ThKattanek/1541-rebuild/doc/fotos/byte_ready_cut_gatearray.jpg

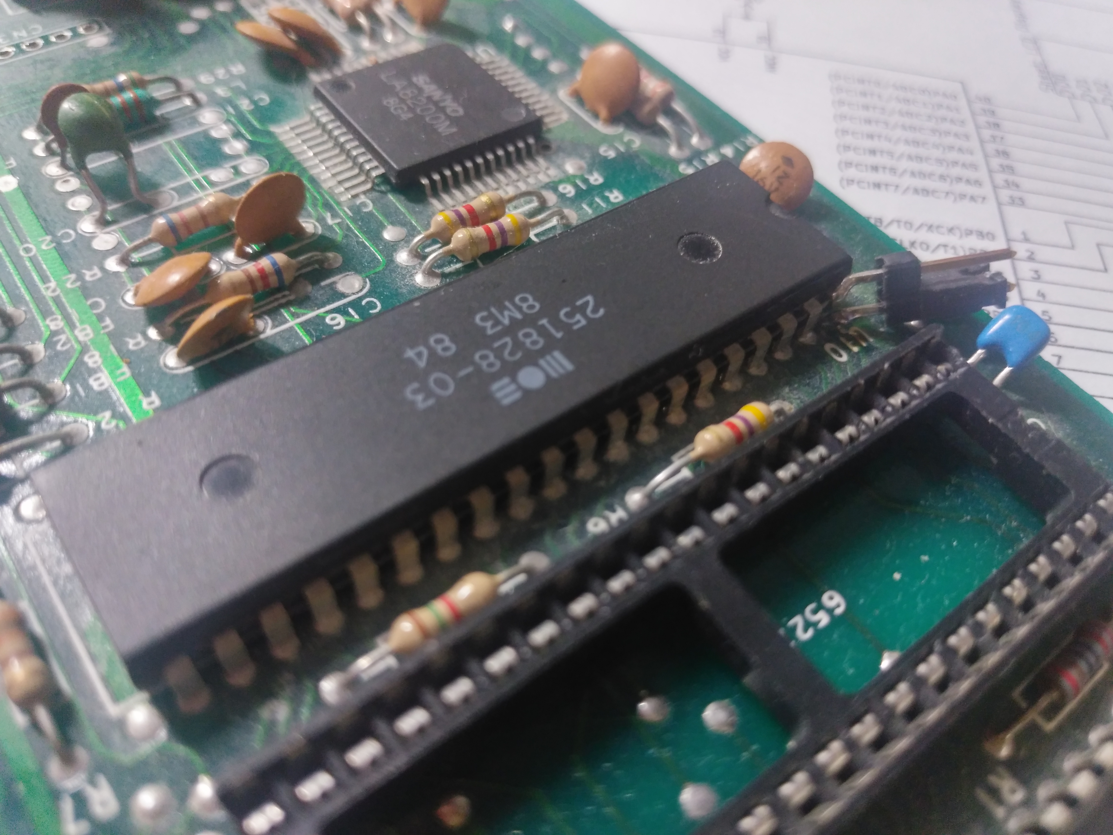
doc/fotos/byte_ready_cut_gatearray.jpg
