ThKattanek/1541-rebuild/doc/fotos/platine_rev_1.4.0/IMG_20200430_232406.jpg

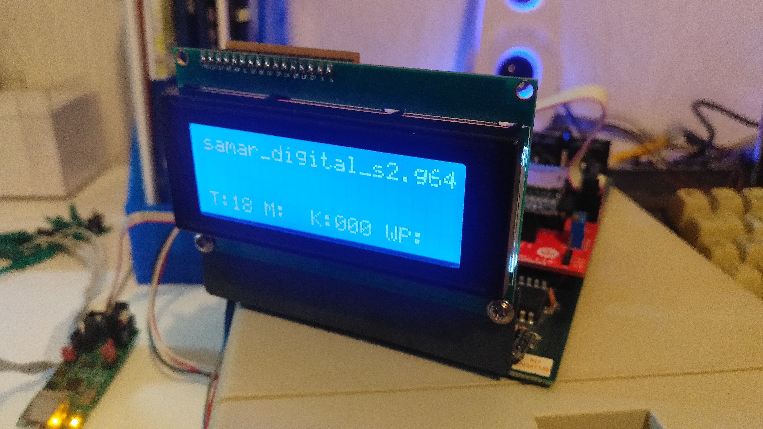
doc/fotos/platine_rev_1.4.0/IMG_20200430_232406.jpg
