ThKattanek/1541-rebuild/doc/fotos/prototyp_lochraster_v1.1/IMG_20180418_214337.jpg

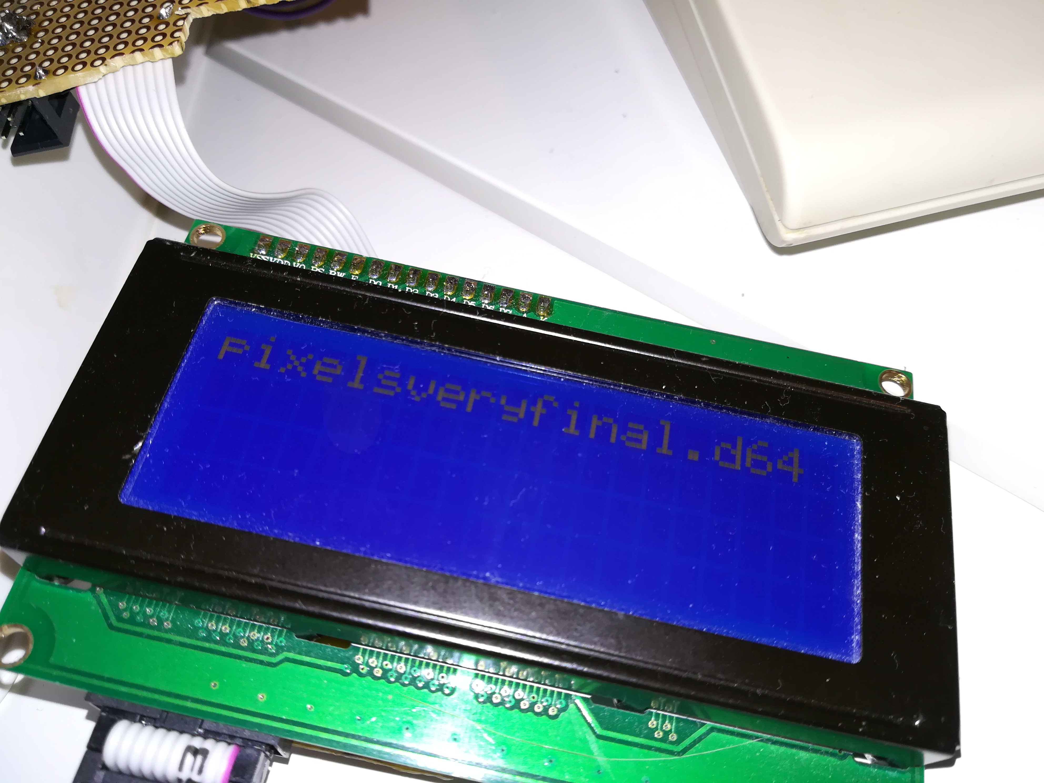
doc/fotos/prototyp_lochraster_v1.1/IMG_20180418_214337.jpg
