ThKattanek/1541-rebuild/doc/gesammelte_infos/1541-II.340503.gif

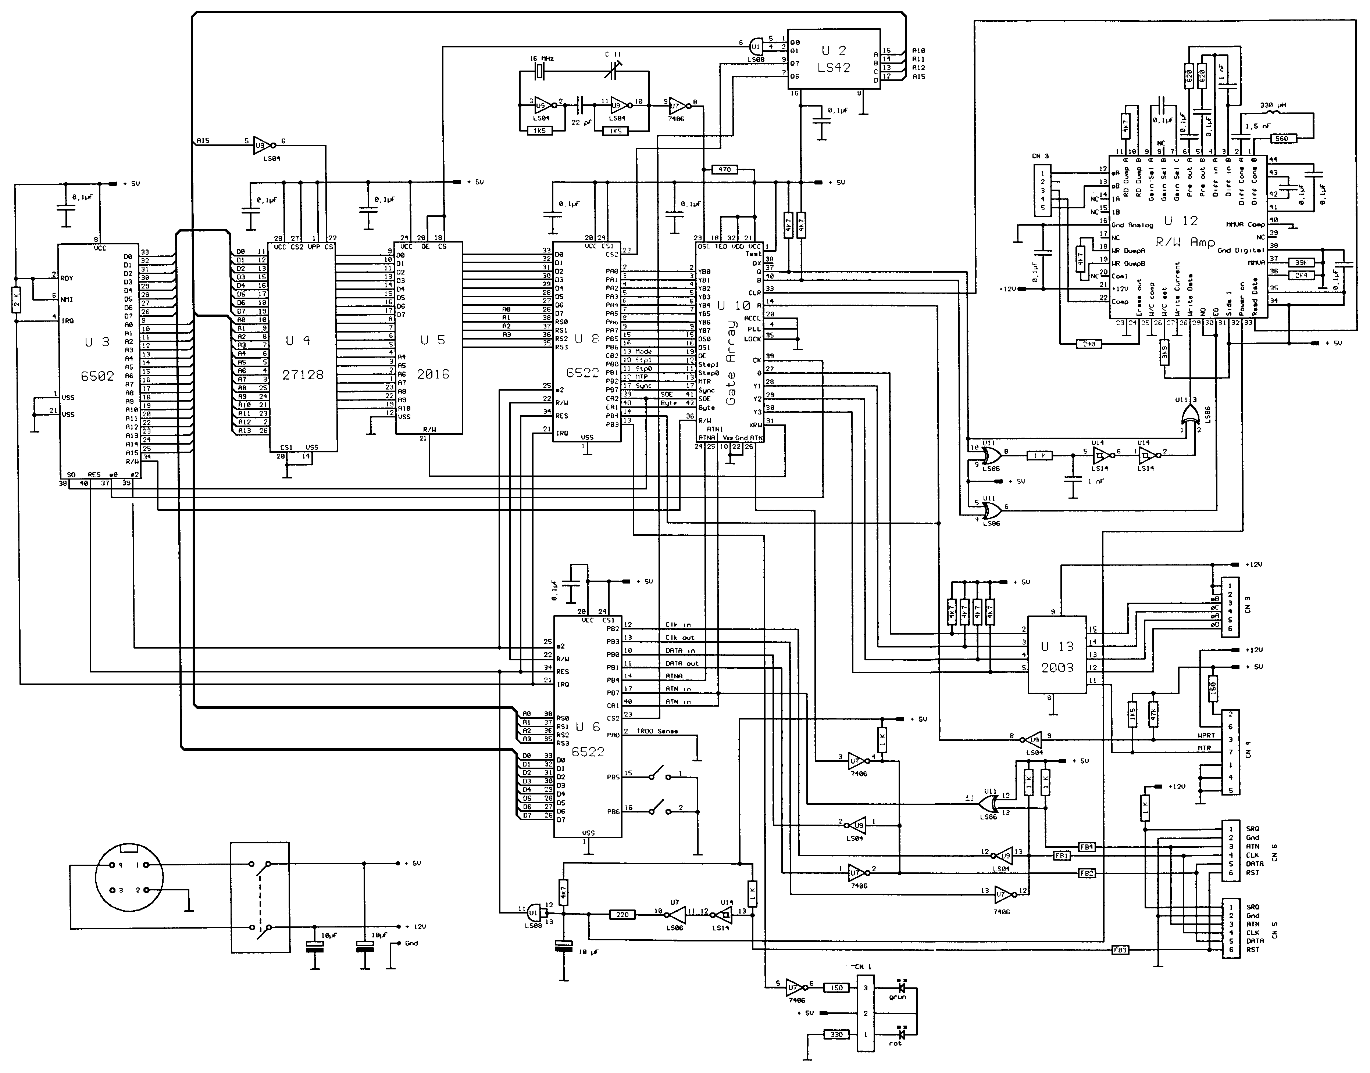
doc/gesammelte_infos/1541-II.340503.gif
