ThKattanek/1541-rebuild/doc/gesammelte_infos/1541-II_Schaltplan.gif

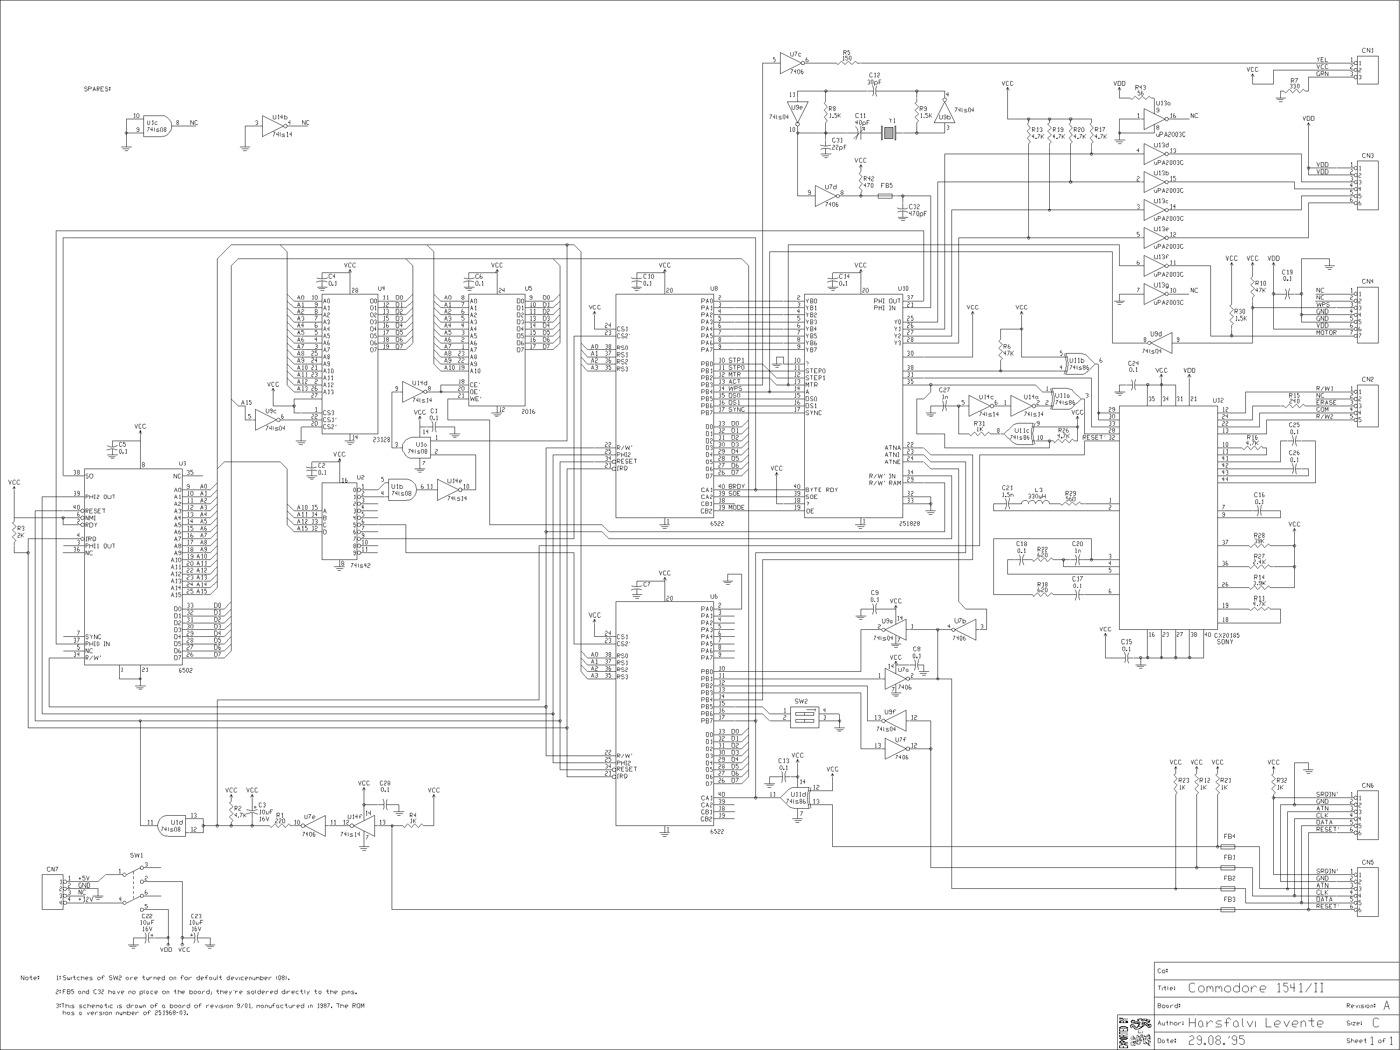
doc/gesammelte_infos/1541-II_Schaltplan.gif
