ThKattanek/1541-rebuild/doc/gesammelte_infos/1541_II_platinenaße_max.jpg

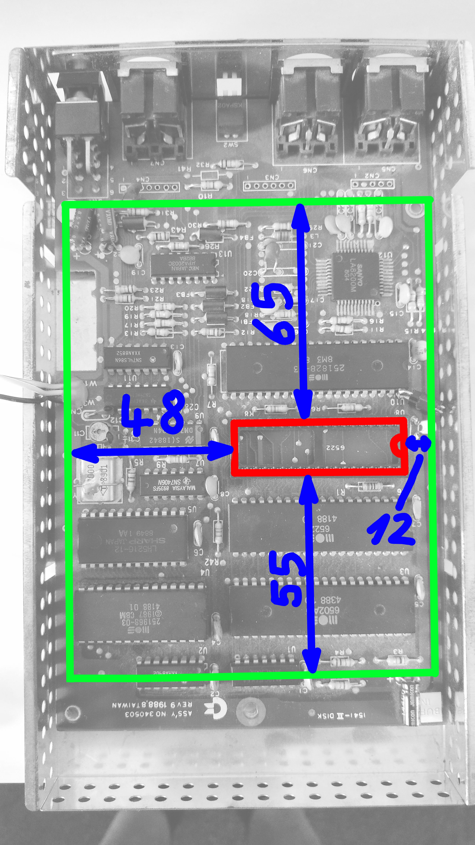
doc/gesammelte_infos/1541_II_platinenaße_max.jpg
