ThKattanek/1541-rebuild/doc/gesammelte_infos/mos_6522/6522-15.gif

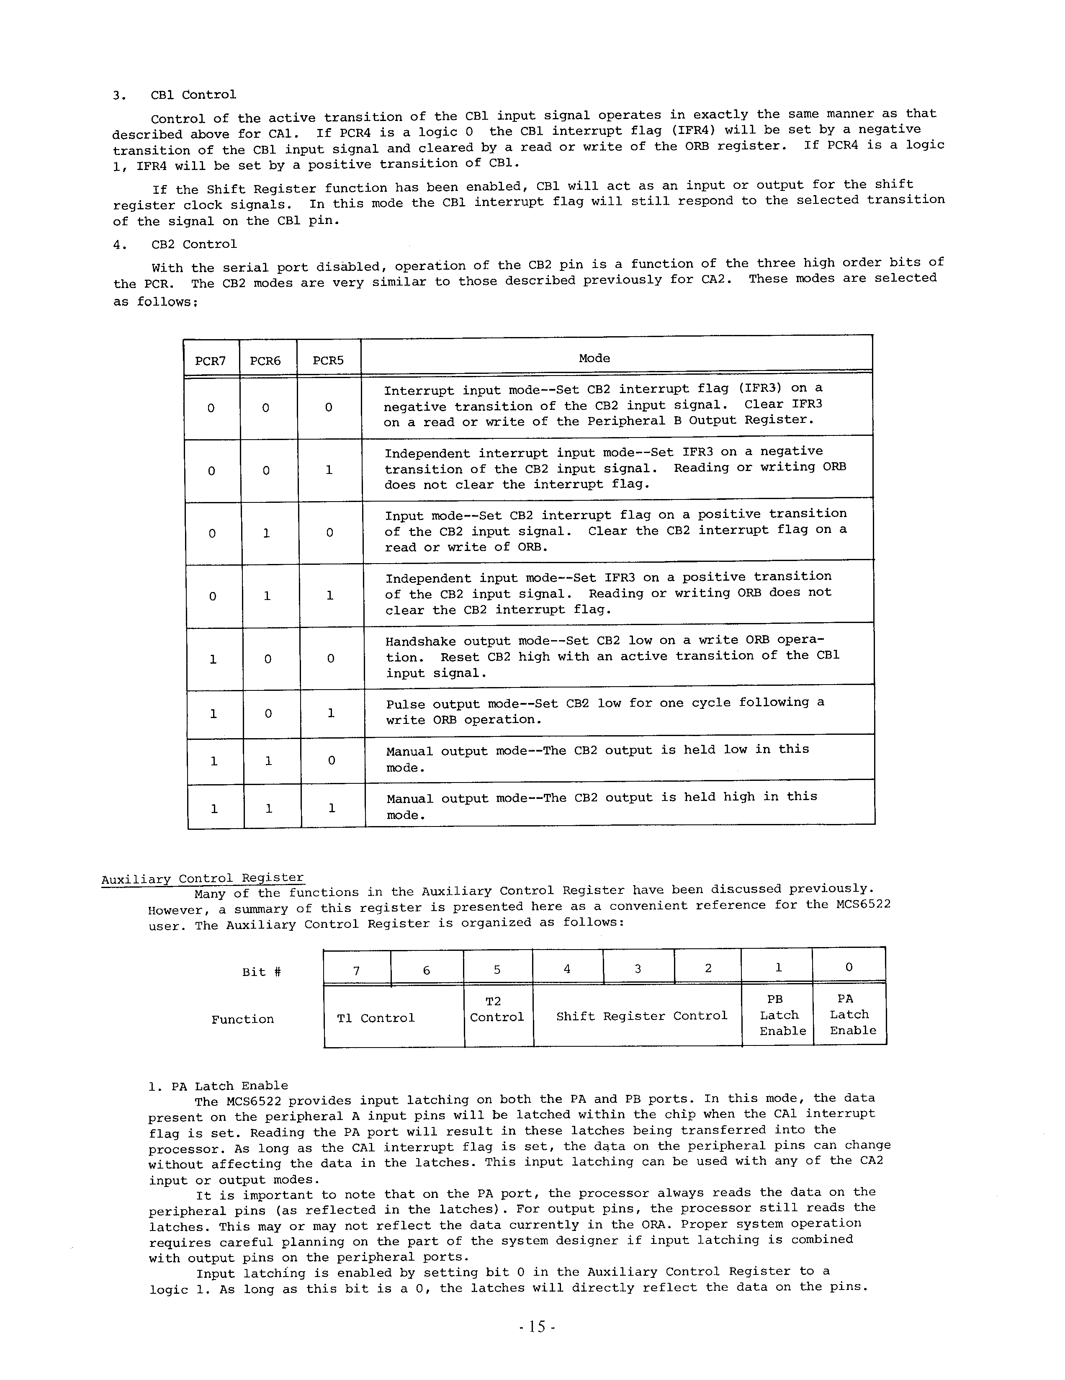
doc/gesammelte_infos/mos_6522/6522-15.gif
