ThKattanek/1541-rebuild/doc/gesammelte_infos/sd_an_microcontroller.jpg

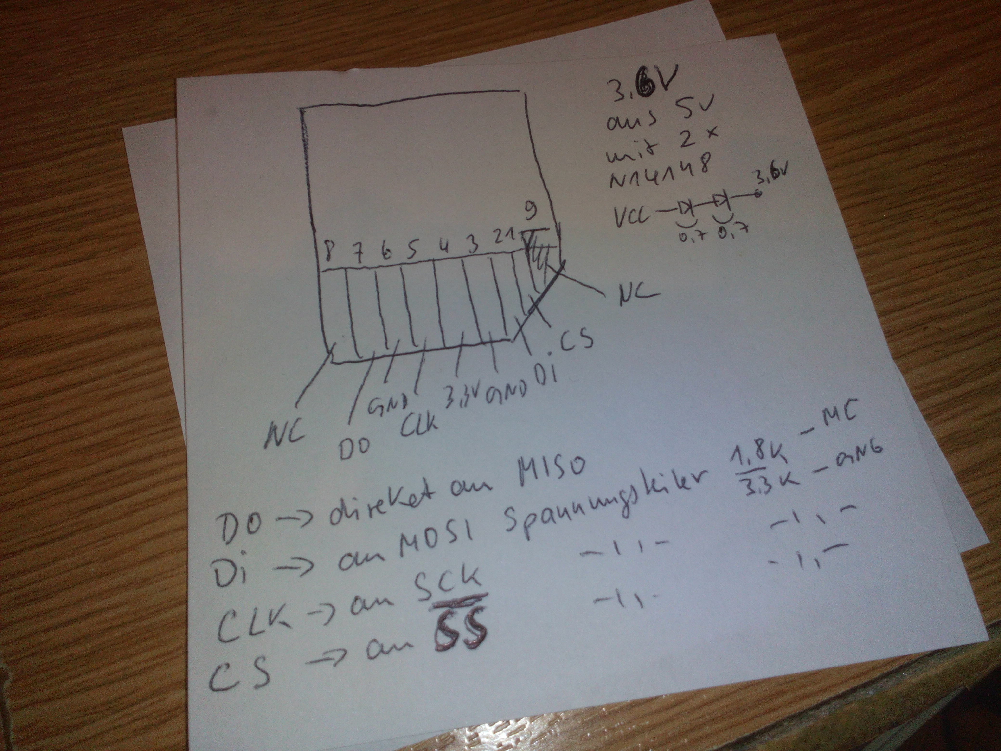
doc/gesammelte_infos/sd_an_microcontroller.jpg
