ThKattanek/1541-rebuild/doc/gesammelte_infos/sd_card_pinbelegung.jpg

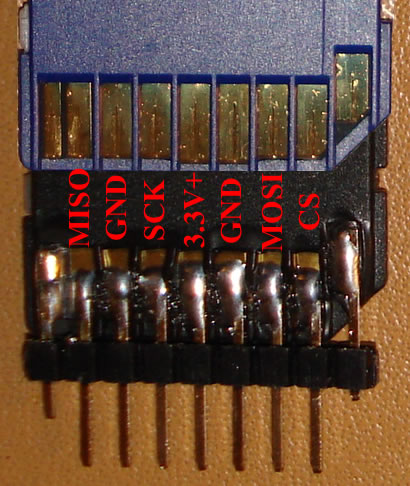
doc/gesammelte_infos/sd_card_pinbelegung.jpg
