ThKattanek/1541-rebuild/doc/oscilloskope_bilder_real_hardware/alle_15ms_wird_SOE_high_im_leerlauf.png

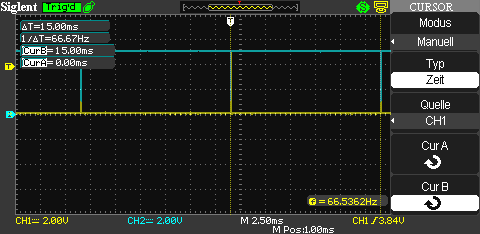
doc/oscilloskope_bilder_real_hardware/alle_15ms_wird_SOE_high_im_leerlauf.png
