ThKattanek/1541-rebuild/doc/oscilloskope_bilder_real_hardware/byte_ready(blau)_und_SOE_im_leerlauf.png

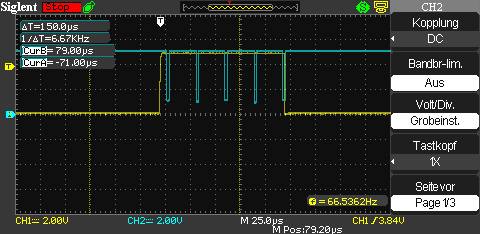
doc/oscilloskope_bilder_real_hardware/byte_ready(blau)_und_SOE_im_leerlauf.png
