ThKattanek/1541-rebuild/doc/oscilloskope_bilder_real_hardware/byte_ready_min_time.png

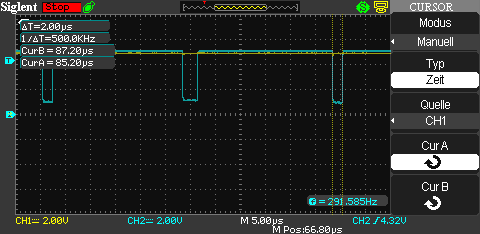
doc/oscilloskope_bilder_real_hardware/byte_ready_min_time.png
