ThKattanek/1541-rebuild/doc/oscilloskope_bilder_real_hardware/byte_ready_time_track18.png

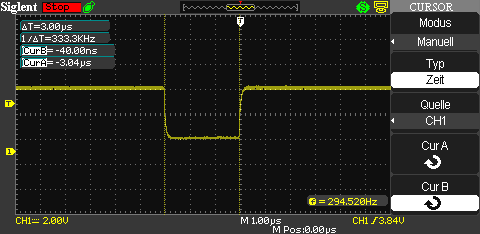
doc/oscilloskope_bilder_real_hardware/byte_ready_time_track18.png
