ThKattanek/1541-rebuild/doc/oscilloskope_bilder_real_hardware/byte_ready_track18_zoom.png

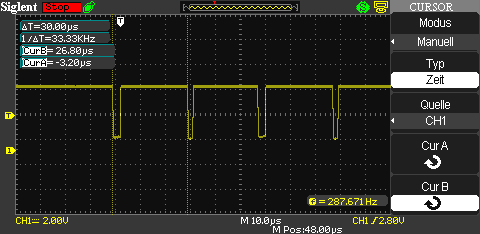
doc/oscilloskope_bilder_real_hardware/byte_ready_track18_zoom.png
