ThKattanek/1541-rebuild/doc/oscilloskope_bilder_real_hardware/sync_track18_abstand_block.png

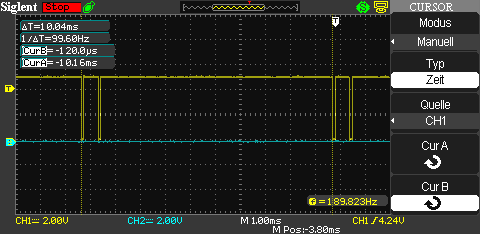
doc/oscilloskope_bilder_real_hardware/sync_track18_abstand_block.png
