ThKattanek/1541-rebuild/doc/oscilloskope_bilder_real_hardware/time_zwischen_2_byte_ready_signale.png

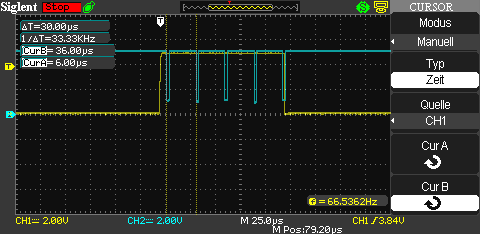
doc/oscilloskope_bilder_real_hardware/time_zwischen_2_byte_ready_signale.png
