ThKattanek/1541-rebuild/doc/oscilloskope_bilder_real_hardware/time_zwischen_sync_header_und_block_track18.png

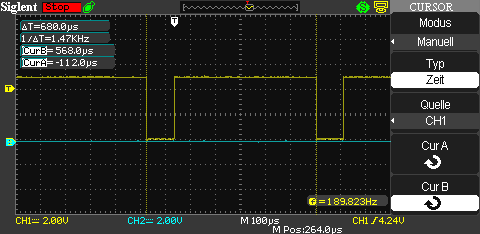
doc/oscilloskope_bilder_real_hardware/time_zwischen_sync_header_und_block_track18.png
