ThKattanek/1541-rebuild/doc/fotos/1541-rebuild.png

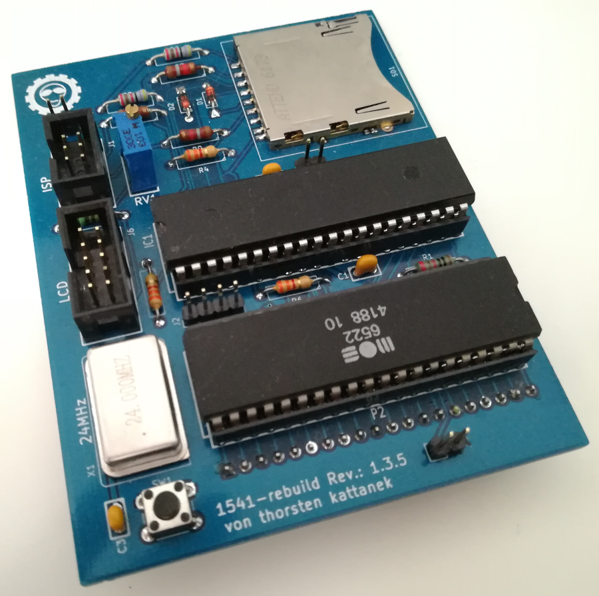
doc/fotos/1541-rebuild.png
