ThKattanek/1541-rebuild/doc/fotos/testaufbau_mit_sd_karte/P9200087.JPG

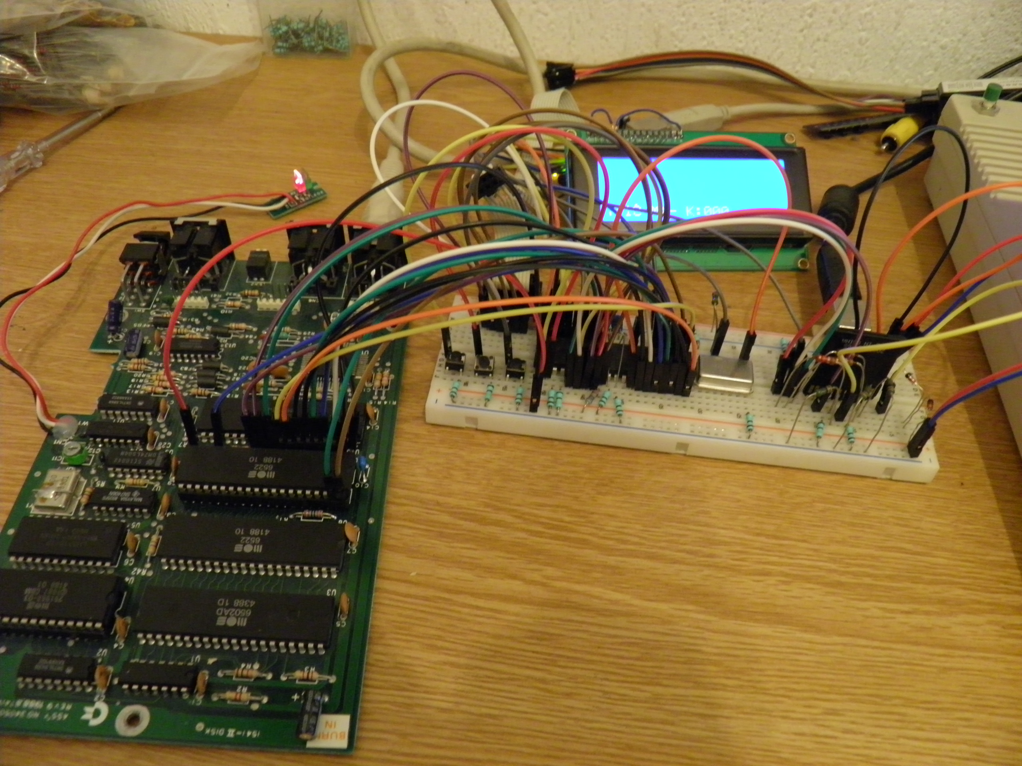
doc/fotos/testaufbau_mit_sd_karte/P9200087.JPG
