ThKattanek/1541-rebuild/doc/fotos/testaufbau_mit_sd_karte/PA010092.JPG

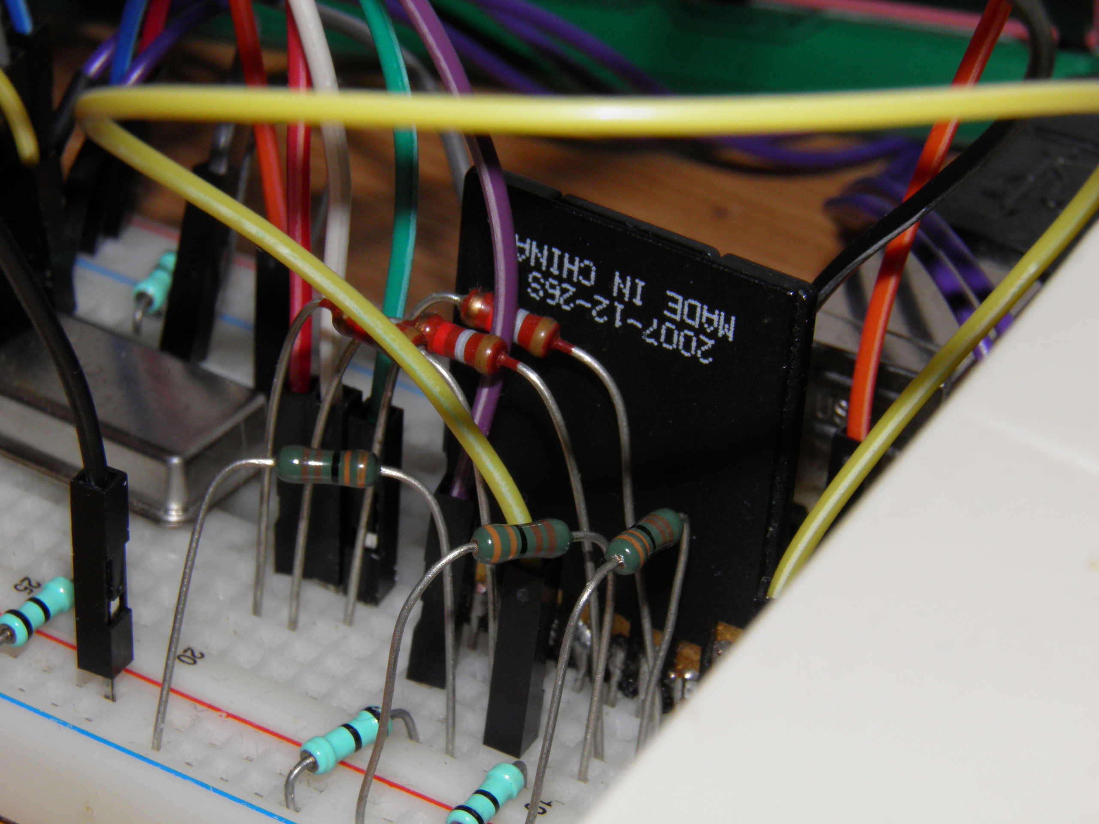
doc/fotos/testaufbau_mit_sd_karte/PA010092.JPG
