ThKattanek/1541-rebuild/doc/fotos/testaufbau_mit_sd_karte/PA010096.JPG

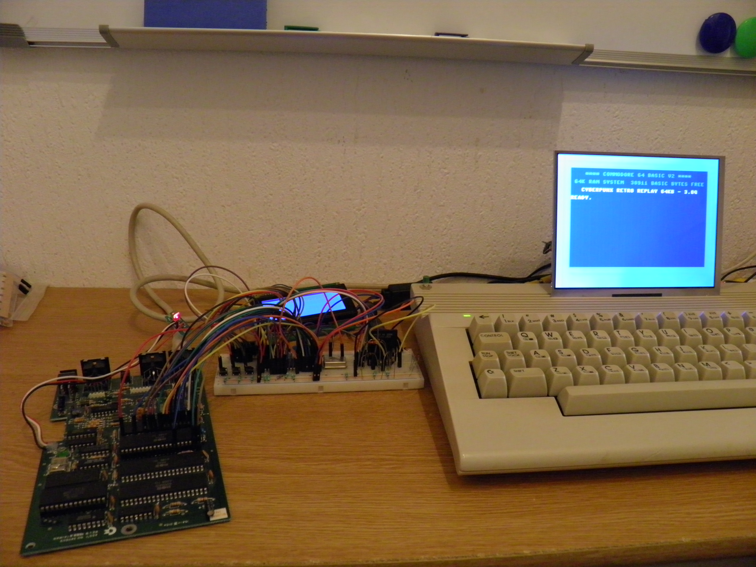
doc/fotos/testaufbau_mit_sd_karte/PA010096.JPG
