ThKattanek/1541-rebuild/doc/fotos/testaufbau_noch_ohne_sd_karte/P9140088.JPG

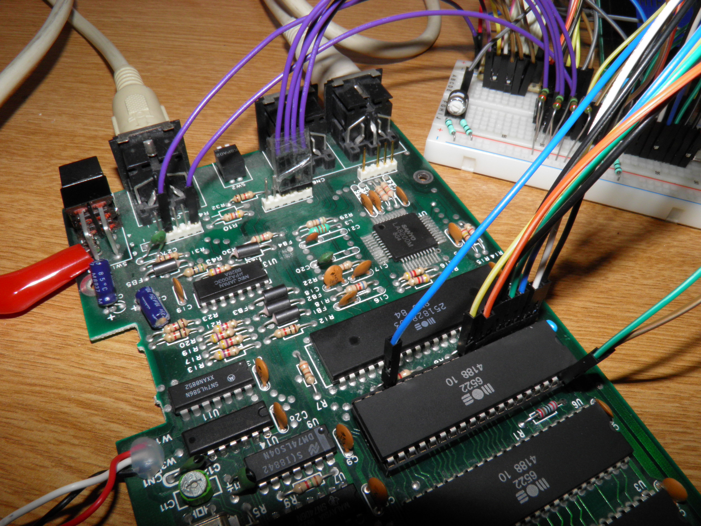
doc/fotos/testaufbau_noch_ohne_sd_karte/P9140088.JPG
